fotherja/Grid_Tie_Inverter_3/GTI_V3_STIDE/Core/Inc/filter1.h

/******************************* SOURCE LICENSE *********************************
Copyright (c) 2021 MicroModeler.

A non-exclusive, nontransferable, perpetual, royalty-free license is granted to the Licensee to 
use the following Information for academic, non-profit, or government-sponsored research purposes.
Use of the following Information under this License is restricted to NON-COMMERCIAL PURPOSES ONLY.
Commercial use of the following Information requires a separately executed written license agreement.

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
******************************* END OF LICENSE *********************************/

// A commercial license for MicroModeler DSP can be obtained at https://www.micromodeler.com/launch.jsp

// Begin header file, filter1.h

#ifndef FILTER1_H_ // Include guards
#define FILTER1_H_

/*
Generated code is based on the following filter design:
<micro.DSP.FilterDocument sampleFrequency="#10000" arithmetic="float" biquads="Direct1" classname="filter1" inputMax="#1" inputShift="#15" >
  <micro.DSP.IirButterworthFilter N="#2" bandType="b" w1="#0.0048" w2="#0.0052" stopbandRipple="#undefined" passbandRipple="#undefined" transitionRatio="#undefined" >
    <micro.DSP.FilterStructure coefficientBits="#0" variableBits="#0" accumulatorBits="#0" biquads="Direct1" >
      <micro.DSP.FilterSection form="Direct1" historyType="Double" accumulatorBits="#0" variableBits="#0" coefficientBits="#0" />
      <micro.DSP.FilterSection form="Direct1" historyType="Double" accumulatorBits="#0" variableBits="#0" coefficientBits="#0" />
    </micro.DSP.FilterStructure>
    <micro.DSP.PoleOrZeroContainer >
      <micro.DSP.PoleOrZero i="#0.030471173837070594" r="#0.9986721853558876" isPoint="#true" isPole="#true" isZero="#false" symmetry="c" N="#1" cascade="#1" />
      <micro.DSP.PoleOrZero i="#0.03224429851618772" r="#0.9985662379391801" isPoint="#true" isPole="#true" isZero="#false" symmetry="c" N="#1" cascade="#0" />
      <micro.DSP.PoleOrZero i="#0" r="#1" isPoint="#true" isPole="#false" isZero="#true" symmetry="r" N="#1" cascade="#1" />
      <micro.DSP.PoleOrZero i="#0" r="#-1" isPoint="#true" isPole="#false" isZero="#true" symmetry="r" N="#1" cascade="#0" />
      <micro.DSP.PoleOrZero i="#0" r="#1" isPoint="#true" isPole="#false" isZero="#true" symmetry="r" N="#1" cascade="#1" />
      <micro.DSP.PoleOrZero i="#0" r="#-1" isPoint="#true" isPole="#false" isZero="#true" symmetry="r" N="#1" cascade="#0" />
    </micro.DSP.PoleOrZeroContainer>
    <micro.DSP.GenericC.CodeGenerator generateTestCases="#false" />
    <micro.DSP.GainControl magnitude="#1" frequency="#0.0048828125" peak="#true" />
  </micro.DSP.IirButterworthFilter>
</micro.DSP.FilterDocument>

*/

static const int filter1_numStages = 2;
static const int filter1_coefficientLength = 10;
extern float filter1_coefficients[10];

typedef struct
{
	float state[8];
	float output;
} filter1Type;

typedef struct
{
    float *pInput;
    float *pOutput;
    float *pState;
    float *pCoefficients;
    short count;
} filter1_executionState;


filter1Type *filter1_create( void );
void filter1_destroy( filter1Type *pObject );
void filter1_init( filter1Type * pThis );
void filter1_reset( filter1Type * pThis );
#define filter1_writeInput( pThis, input )  \
    filter1_filterBlock( pThis, &(input), &(pThis)->output, 1 );

#define filter1_readOutput( pThis )  \
    (pThis)->output

int filter1_filterBlock( filter1Type * pThis, float * pInput, float * pOutput, unsigned int count );
#define filter1_outputToFloat( output )  \
    (output)

#define filter1_inputFromFloat( input )  \
    (input)

void filter1_filterBiquad( filter1_executionState * pExecState );
#endif // FILTER1_H_
	

	
