fotherja/Grid_Tie_Inverter_3/GTI_V3_STIDE/Core/Src/filter1.c

/******************************* SOURCE LICENSE *********************************
Copyright (c) 2021 MicroModeler.

A non-exclusive, nontransferable, perpetual, royalty-free license is granted to the Licensee to 
use the following Information for academic, non-profit, or government-sponsored research purposes.
Use of the following Information under this License is restricted to NON-COMMERCIAL PURPOSES ONLY.
Commercial use of the following Information requires a separately executed written license agreement.

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
******************************* END OF LICENSE *********************************/

// A commercial license for MicroModeler DSP can be obtained at https://www.micromodeler.com/launch.jsp

#include "filter1.h"

#include <stdlib.h> // For malloc/free
#include <string.h> // For memset

float filter1_coefficients[10] = 
{
// Scaled for floating point

    0.000013270715580081536, 0.000026541431160163073, 0.000013270715580081536, 1.9971324758783602, -0.9981742263388083,// b0, b1, b2, a1, a2
    0.125, -0.25, 0.125, 1.9973443707117753, -0.9982746262385134// b0, b1, b2, a1, a2

};


filter1Type *filter1_create( void )
{
    filter1Type *result = (filter1Type *)malloc( sizeof( filter1Type ) ); // Allocate memory for the object
    filter1_init( result );                                               // Initialize it
    return result;                                                        // Return the result
}

void filter1_destroy( filter1Type *pObject )
{
    free( pObject );
}

void filter1_init( filter1Type * pThis )
{
    filter1_reset( pThis );
}

void filter1_reset( filter1Type * pThis )
{
    memset( &pThis->state, 0, sizeof( pThis->state ) ); // Reset state to 0
    pThis->output = 0;                                    // Reset output
}

int filter1_filterBlock( filter1Type * pThis, float * pInput, float * pOutput, unsigned int count )
{
    filter1_executionState executionState;          // The executionState structure holds call data, minimizing stack reads and writes 
    if( ! count ) return 0;                         // If there are no input samples, return immediately
    executionState.pInput = pInput;                 // Pointers to the input and output buffers that each call to filterBiquad() will use
    executionState.pOutput = pOutput;               // - pInput and pOutput can be equal, allowing reuse of the same memory.
    executionState.count = count;                   // The number of samples to be processed
    executionState.pState = pThis->state;                   // Pointer to the biquad's internal state and coefficients. 
    executionState.pCoefficients = filter1_coefficients;    // Each call to filterBiquad() will advance pState and pCoefficients to the next biquad

    // The 1st call to filter1_filterBiquad() reads from the caller supplied input buffer and writes to the output buffer.
    // The remaining calls to filterBiquad() recycle the same output buffer, so that multiple intermediate buffers are not required.

    filter1_filterBiquad( &executionState );		// Run biquad #0
    executionState.pInput = executionState.pOutput;         // The remaining biquads will now re-use the same output buffer.

    filter1_filterBiquad( &executionState );		// Run biquad #1

    // At this point, the caller-supplied output buffer will contain the filtered samples and the input buffer will contain the unmodified input samples.  
    return count;		// Return the number of samples processed, the same as the number of input samples
}

void filter1_filterBiquad( filter1_executionState * pExecState )
{

    // Read state variables
    float x0;
    float x1 = pExecState->pState[0];
    float x2 = pExecState->pState[1];
    float y1 = pExecState->pState[2];
    float y2 = pExecState->pState[3];

    // Read coefficients into work registers
    float b0 = *(pExecState->pCoefficients++);
    float b1 = *(pExecState->pCoefficients++);
    float b2 = *(pExecState->pCoefficients++);
    float a1 = *(pExecState->pCoefficients++);
    float a2 = *(pExecState->pCoefficients++);

    // Read source and target pointers
    float *pInput  = pExecState->pInput;
    float *pOutput = pExecState->pOutput;
    short count = pExecState->count;
    float accumulator;

    while( count-- )
    {
        x0 = *(pInput++);

        accumulator  = x2 * b2;
        accumulator += x1 * b1;
        accumulator += x0 * b0;

        x2 = x1;        // Shuffle left history buffer
        x1 = x0;

        accumulator += y2 * a2;
        accumulator += y1 * a1;

        y2 = y1;        // Shuffle right history buffer
        y1 = accumulator ;

        *(pOutput++) = accumulator ;
    }

    *(pExecState->pState++) = x1;
    *(pExecState->pState++) = x2;
    *(pExecState->pState++) = y1;
    *(pExecState->pState++) = y2;
   
}
